Fr3nchT0uch/AY-3-8913_to_AY-3-8910_Adapter/Normal/Medias/adapter 8913-8910 C1.png

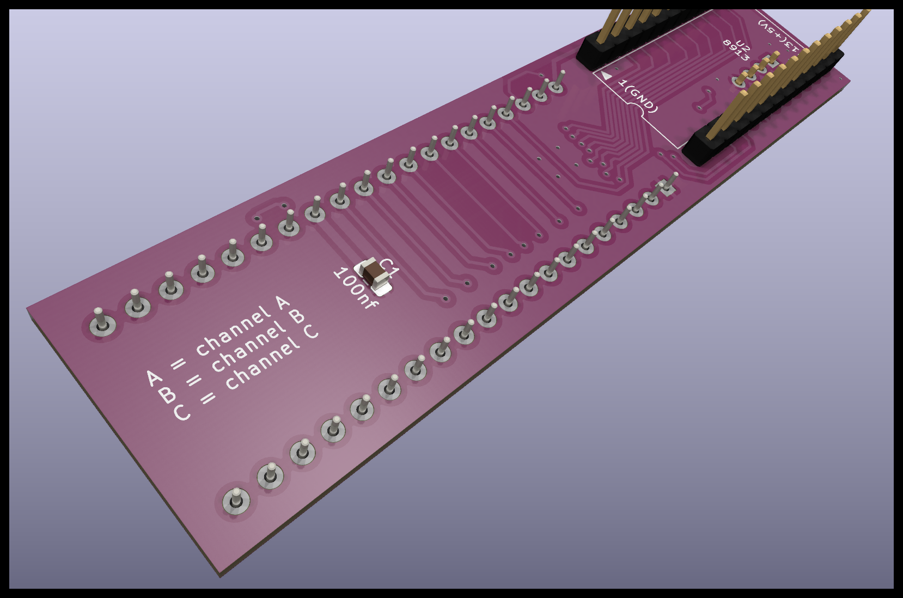
Normal/Medias/adapter 8913-8910 C1.png
